proboterror/SMD2GC/src/hid_dumps.h

#pragma once

#include <stdint.h>

// https://github.com/DJm00n/ControllersInfo/tree/master/dualshock4

// array size is 507
static const uint8_t dualshock4_hid_report_descriptor[] = {
  0x05, 0x01, 0x09, 0x05, 0xa1, 0x01, 0x85, 0x01, 0x09, 0x30, 0x09, 0x31, 0x09, 0x32, 0x09, 0x35,
  0x15, 0x00, 0x26, 0xff, 0x00, 0x75, 0x08, 0x95, 0x04, 0x81, 0x02, 0x09, 0x39, 0x15, 0x00, 0x25,
  0x07, 0x35, 0x00, 0x46, 0x3b, 0x01, 0x65, 0x14, 0x75, 0x04, 0x95, 0x01, 0x81, 0x42, 0x65, 0x00,
  0x05, 0x09, 0x19, 0x01, 0x29, 0x0e, 0x15, 0x00, 0x25, 0x01, 0x75, 0x01, 0x95, 0x0e, 0x81, 0x02,
  0x06, 0x00, 0xff, 0x09, 0x20, 0x75, 0x06, 0x95, 0x01, 0x15, 0x00, 0x25, 0x7f, 0x81, 0x02, 0x05,
  0x01, 0x09, 0x33, 0x09, 0x34, 0x15, 0x00, 0x26, 0xff, 0x00, 0x75, 0x08, 0x95, 0x02, 0x81, 0x02,
  0x06, 0x00, 0xff, 0x09, 0x21, 0x95, 0x36, 0x81, 0x02, 0x85, 0x05, 0x09, 0x22, 0x95, 0x1f, 0x91,
  0x02, 0x85, 0x04, 0x09, 0x23, 0x95, 0x24, 0xb1, 0x02, 0x85, 0x02, 0x09, 0x24, 0x95, 0x24, 0xb1,
  0x02, 0x85, 0x08, 0x09, 0x25, 0x95, 0x03, 0xb1, 0x02, 0x85, 0x10, 0x09, 0x26, 0x95, 0x04, 0xb1,
  0x02, 0x85, 0x11, 0x09, 0x27, 0x95, 0x02, 0xb1, 0x02, 0x85, 0x12, 0x06, 0x02, 0xff, 0x09, 0x21,
  0x95, 0x0f, 0xb1, 0x02, 0x85, 0x13, 0x09, 0x22, 0x95, 0x16, 0xb1, 0x02, 0x85, 0x14, 0x06, 0x05,
  0xff, 0x09, 0x20, 0x95, 0x10, 0xb1, 0x02, 0x85, 0x15, 0x09, 0x21, 0x95, 0x2c, 0xb1, 0x02, 0x06,
  0x80, 0xff, 0x85, 0x80, 0x09, 0x20, 0x95, 0x06, 0xb1, 0x02, 0x85, 0x81, 0x09, 0x21, 0x95, 0x06,
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
	0x00, 0xFC, 0xFF, 0x72, 0x01, 0x6F, 0x1A, 0x3F, 0xF0, 0x00, 0x00, 0x00, 0x00, 0x00, 0x1B, 0x00,
	0x00, 0x01, 0x72, 0x81, 0x37, 0x87, 0x05, 0x80, 0x00, 0x00, 0x00, 0x00, 0x80, 0x00, 0x00, 0x00,
	0x80, 0x00, 0x00, 0x00, 0x00, 0x80, 0x00, 0x00, 0x00, 0x80, 0x00, 0x00, 0x00, 0x00, 0x80, 0x00
};

static const uint8_t my_dualshock_4_hid_report_lx_rx_min[] = {
	0x01, 0x00, 0x5E, 0x00, 0x7F, 0x08, 0x00, 0xA8, 0x00, 0x00, 0x11, 0x05, 0x08, 0x07, 0x00, 0x03,
	0x00, 0xF4, 0xFF, 0xDC, 0x01, 0x91, 0x1F, 0x28, 0x04, 0x00, 0x00, 0x00, 0x00, 0x00, 0x1B, 0x00,
	0x00, 0x00, 0x00, 0x80, 0x00, 0x00, 0x00, 0x80, 0x00, 0x00, 0x00, 0x00, 0x80, 0x00, 0x00, 0x00,
	0x80, 0x00, 0x00, 0x00, 0x00, 0x80, 0x00, 0x00, 0x00, 0x80, 0x00, 0x00, 0x00, 0x00, 0x80, 0x00
};

static const uint8_t my_dualshock_4_hid_report_idle[] = {
	0x01, 0x7E, 0x83, 0x7E, 0x7F, 0x08, 0x00, 0xA8, 0x00, 0x00, 0x3E, 0x48, 0x03, 0x25, 0x00, 0x02,
	0x00, 0xDA, 0xFF, 0x9F, 0xFA, 0x4F, 0x1D, 0x55, 0xF6, 0x00, 0x00, 0x00, 0x00, 0x00, 0x1B, 0x00,
	0x00, 0x01, 0x65, 0x01, 0x48, 0x01, 0x00, 0x80, 0x00, 0x00, 0x00, 0x00, 0x80, 0x00, 0x00, 0x00,
	0x80, 0x00, 0x00, 0x00, 0x00, 0x80, 0x00, 0x00, 0x00, 0x80, 0x00, 0x00, 0x00, 0x00, 0x80, 0x00
};

// https://gimx.fr/wiki/index.php?title=DualShock_4#Sample_Report

static const uint8_t dualshock_4_hid_report_descriptor_gimx_fr_wiki[] = {
0x05, 0x01,        // Usage Page (Generic Desktop Ctrls)
0x09, 0x05,        // Usage (Game Pad)
0xA1, 0x01,        // Collection (Application)
0x85, 0x01,        //   Report ID (1)
0x09, 0x30,        //   Usage (X)
0x09, 0x31,        //   Usage (Y)
0x09, 0x32,        //   Usage (Z)
0x09, 0x35,        //   Usage (Rz)
0x15, 0x00,        //   Logical Minimum (0)
0x26, 0xFF, 0x00,  //   Logical Maximum (255)
0x75, 0x08,        //   Report Size (8)
0x95, 0x04,        //   Report Count (4)
0x81, 0x02,        //   Input (Data,Var,Abs,No Wrap,Linear,Preferred State,No Null Position)
0x09, 0x39,        //   Usage (Hat switch)
0x15, 0x00,        //   Logical Minimum (0)
0x25, 0x07,        //   Logical Maximum (7)
0x35, 0x00,        //   Physical Minimum (0)
0x46, 0x3B, 0x01,  //   Physical Maximum (315)
0x65, 0x14,        //   Unit (System: English Rotation, Length: Centimeter)
0x75, 0x04,        //   Report Size (4)
0x95, 0x01,        //   Report Count (1)
0x81, 0x42,        //   Input (Data,Var,Abs,No Wrap,Linear,Preferred State,Null State)
0x65, 0x00,        //   Unit (None)
0x05, 0x09,        //   Usage Page (Button)
0x19, 0x01,        //   Usage Minimum (0x01)
0x29, 0x0E,        //   Usage Maximum (0x0E)
0x15, 0x00,        //   Logical Minimum (0)
0x25, 0x01,        //   Logical Maximum (1)
0x75, 0x01,        //   Report Size (1)
0x95, 0x0E,        //   Report Count (14)
0x81, 0x02,        //   Input (Data,Var,Abs,No Wrap,Linear,Preferred State,No Null Position)
0x06, 0x00, 0xFF,  //   Usage Page (Vendor Defined 0xFF00)
0x09, 0x20,        //   Usage (0x20)
0x75, 0x06,        //   Report Size (6)
0x95, 0x01,        //   Report Count (1)
0x15, 0x00,        //   Logical Minimum (0)
0x25, 0x7F,        //   Logical Maximum (127)
0x81, 0x02,        //   Input (Data,Var,Abs,No Wrap,Linear,Preferred State,No Null Position)
0x05, 0x01,        //   Usage Page (Generic Desktop Ctrls)
0x09, 0x33,        //   Usage (Rx)
0x09, 0x34,        //   Usage (Ry)
0x15, 0x00,        //   Logical Minimum (0)
0x26, 0xFF, 0x00,  //   Logical Maximum (255)
0x75, 0x08,        //   Report Size (8)
0x95, 0x02,        //   Report Count (2)
0x81, 0x02,        //   Input (Data,Var,Abs,No Wrap,Linear,Preferred State,No Null Position)
0x06, 0x00, 0xFF,  //   Usage Page (Vendor Defined 0xFF00)
0x09, 0x21,        //   Usage (0x21)
0x95, 0x36,        //   Report Count (54)
0x81, 0x02,        //   Input (Data,Var,Abs,No Wrap,Linear,Preferred State,No Null Position)
0x85, 0x05,        //   Report ID (5)
0x09, 0x22,        //   Usage (0x22)
0x95, 0x1F,        //   Report Count (31)
0x91, 0x02,        //   Output (Data,Var,Abs,No Wrap,Linear,Preferred State,No Null Position,Non-volatile)
0x85, 0x04,        //   Report ID (4)
0x09, 0x23,        //   Usage (0x23)
0x95, 0x24,        //   Report Count (36)
0xB1, 0x02,        //   Feature (Data,Var,Abs,No Wrap,Linear,Preferred State,No Null Position,Non-volatile)
0x85, 0x02,        //   Report ID (2)
0x09, 0x24,        //   Usage (0x24)
0x95, 0x24,        //   Report Count (36)
0xB1, 0x02,        //   Feature (Data,Var,Abs,No Wrap,Linear,Preferred State,No Null Position,Non-volatile)
0x85, 0x08,        //   Report ID (8)
0x09, 0x25,        //   Usage (0x25)
0x95, 0x03,        //   Report Count (3)
0xB1, 0x02,        //   Feature (Data,Var,Abs,No Wrap,Linear,Preferred State,No Null Position,Non-volatile)
0x85, 0x10,        //   Report ID (16)
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
0x95, 0x01,        //   Report Count (1)
0xB1, 0x02,        //   Feature (Data,Var,Abs,No Wrap,Linear,Preferred State,No Null Position,Non-volatile)
0x85, 0xA9,        //   Report ID (169)
0x09, 0x4C,        //   Usage (0x4C)
0x95, 0x08,        //   Report Count (8)
0xB1, 0x02,        //   Feature (Data,Var,Abs,No Wrap,Linear,Preferred State,No Null Position,Non-volatile)
0x85, 0xAA,        //   Report ID (170)
0x09, 0x4E,        //   Usage (0x4E)
0x95, 0x01,        //   Report Count (1)
0xB1, 0x02,        //   Feature (Data,Var,Abs,No Wrap,Linear,Preferred State,No Null Position,Non-volatile)
0x85, 0xAB,        //   Report ID (171)
0x09, 0x4F,        //   Usage (0x4F)
0x95, 0x39,        //   Report Count (57)
0xB1, 0x02,        //   Feature (Data,Var,Abs,No Wrap,Linear,Preferred State,No Null Position,Non-volatile)
0x85, 0xAC,        //   Report ID (172)
0x09, 0x50,        //   Usage (0x50)
0x95, 0x39,        //   Report Count (57)
0xB1, 0x02,        //   Feature (Data,Var,Abs,No Wrap,Linear,Preferred State,No Null Position,Non-volatile)
0x85, 0xAD,        //   Report ID (173)
0x09, 0x51,        //   Usage (0x51)
0x95, 0x0B,        //   Report Count (11)
0xB1, 0x02,        //   Feature (Data,Var,Abs,No Wrap,Linear,Preferred State,No Null Position,Non-volatile)
0x85, 0xAE,        //   Report ID (174)
0x09, 0x52,        //   Usage (0x52)
0x95, 0x01,        //   Report Count (1)
0xB1, 0x02,        //   Feature (Data,Var,Abs,No Wrap,Linear,Preferred State,No Null Position,Non-volatile)
0x85, 0xAF,        //   Report ID (175)
0x09, 0x53,        //   Usage (0x53)
0x95, 0x02,        //   Report Count (2)
0xB1, 0x02,        //   Feature (Data,Var,Abs,No Wrap,Linear,Preferred State,No Null Position,Non-volatile)
0x85, 0xB0,        //   Report ID (176)
0x09, 0x54,        //   Usage (0x54)
0x95, 0x3F,        //   Report Count (63)
0xB1, 0x02,        //   Feature (Data,Var,Abs,No Wrap,Linear,Preferred State,No Null Position,Non-volatile)
0xC0               // End Collection
};
// 467 bytes

static const uint8_t dualshock_4_hid_report_gimx_fr_wiki[] = {
	0x01, 0x81, 0x80, 0x83, 0x7A, 0x08, 0x00, 0x00, 0x00, 0x00, 0x93, 0x5F, 0xFB, 0xD2, 0xFF, 0xDA,
	0xFF, 0xD8, 0xFF, 0x4F, 0xEE, 0x14, 0x1B, 0x99, 0xFE, 0x00, 0x00, 0x00, 0x00, 0x00, 0x05, 0x00,
	0x00, 0x00, 0x00, 0x80, 0x00, 0x00, 0x00, 0x80, 0x00, 0x00, 0x00, 0x00, 0x80, 0x00, 0x00, 0x00,
	0x80, 0x00, 0x00, 0x00, 0x00, 0x80, 0x00, 0x00, 0x00, 0x80, 0x00, 0x00, 0x00, 0x00, 0x80, 0x00,
};

// DualShock 3 CECHZC2R
static const uint8_t dualshock_3_hid_report_descriptor[] = {
	0x05, 0x01, 0x09, 0x04, 0xA1, 0x01, 0xA1, 0x02, 0x85, 0x01, 0x75, 0x08, 0x95, 0x01, 0x15, 0x00,
	0x26, 0xFF, 0x00, 0x81, 0x03, 0x75, 0x01, 0x95, 0x13, 0x15, 0x00, 0x25, 0x01, 0x35, 0x00, 0x45,
	0x01, 0x05, 0x09, 0x19, 0x01, 0x29, 0x13, 0x81, 0x02, 0x75, 0x01, 0x95, 0x0D, 0x06, 0x00, 0xFF,
	0x81, 0x03, 0x15, 0x00, 0x26, 0xFF, 0x00, 0x05, 0x01, 0x09, 0x01, 0xA1, 0x00, 0x75, 0x08, 0x95,
	0x04, 0x35, 0x00, 0x46, 0xFF, 0x00, 0x09, 0x30, 0x09, 0x31, 0x09, 0x32, 0x09, 0x35, 0x81, 0x02,
	0xC0, 0x05, 0x01, 0x75, 0x08, 0x95, 0x27, 0x09, 0x01, 0x81, 0x02, 0x75, 0x08, 0x95, 0x30, 0x09,
	0x01, 0x91, 0x02, 0x75, 0x08, 0x95, 0x30, 0x09, 0x01, 0xB1, 0x02, 0xC0, 0xA1, 0x02, 0x85, 0x02,
	0x75, 0x08, 0x95, 0x30, 0x09, 0x01, 0xB1, 0x02, 0xC0, 0xA1, 0x02, 0x85, 0xEE, 0x75, 0x08, 0x95,
	0x30, 0x09, 0x01, 0xB1, 0x02, 0xC0, 0xA1, 0x02, 0x85, 0xEF, 0x75, 0x08, 0x95, 0x30, 0x09, 0x01,
	0xB1, 0x02, 0xC0, 0xC0
};

// PS5 DualSence CFI-ZCT1W
static const uint8_t dualsence_hid_report_descriptor[] = {
	0x05, 0x01, 0x09, 0x05, 0xA1, 0x01, 0x85, 0x01, 0x09, 0x30, 0x09, 0x31, 0x09, 0x32, 0x09, 0x35,
	0x09, 0x33, 0x09, 0x34, 0x15, 0x00, 0x26, 0xFF, 0x00, 0x75, 0x08, 0x95, 0x06, 0x81, 0x02, 0x06,
	0x00, 0xFF, 0x09, 0x20, 0x95, 0x01, 0x81, 0x02, 0x05, 0x01, 0x09, 0x39, 0x15, 0x00, 0x25, 0x07,
	0x35, 0x00, 0x46, 0x3B, 0x01, 0x65, 0x14, 0x75, 0x04, 0x95, 0x01, 0x81, 0x42, 0x65, 0x00, 0x05,
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
	0xFD, 0xFF, 0x02, 0x00, 0xFE, 0xFF, 0x49, 0x01, 0xAE, 0x1F, 0x74, 0x03, 0x4D, 0x2A, 0xA8, 0x74,
	0x08, 0x80, 0x2B, 0x57, 0x1A, 0x80, 0x00, 0x00, 0x00, 0xD5, 0x09, 0x09, 0x00, 0x00, 0x00, 0x00,
	0x00, 0x70, 0xBA, 0xA8, 0x74, 0x28, 0x08, 0x00, 0x64, 0x7D, 0x33, 0x47, 0x63, 0xD8, 0xD5, 0x2F
};
